wavefarm/Internet-Radio-Toolkit/Arduino/InternetRadioSketch/src/ToolkitFiles/ToolkitFiles.cpp

//
// ToolkitFiles.cpp

#include <FS.h>

//#include <LittleFS.h>
//#define TOOLFS LittleFS

//#include <LITTLEFS.h>
//#define TOOLFS LITTLEFS

#include "../ToolkitLittleFS/ToolkitLittleFS.h"
#define TOOLFS ToolkitLittleFS

#include "ToolkitFiles.h"

boolean ToolkitFiles::begin()
{
    if (!TOOLFS.begin(false)) {
        Serial.println("Flash Storage will be reformatted!");
        Serial.println("This may take a while ..");
        if (!TOOLFS.format()) {
            Serial.println("Error formatting Flash Storage!");
            return false;
        } else { // formatted okay
            delay(100);
            return TOOLFS.begin(false);
        }
    }
    return true; // formats the flash if it isn't formatted
} // returns false if the file system doesn't mount

//
// Some DOCS:
//
// size_t actual = file.readBytes(char *buffer, size_t length);
// int avail = file.available(); .. not sure if this is the same as filesize
// void file.close();
// boolean file.isDirectory();
// size_t file.size();
// size_t file.write(char *buffer, size_t length);
//
// boolean FS.exists(const char *path);
// File FS.open(const char *path, int mode=FILE_READ, const bool create=false);
// mode can also be FILE_WRITE or FILE_APPEND
// NOTE: the headers available online differ from the headers used by the IDE
// bool create is not part of the open() prototype!

boolean ToolkitFiles::fileExists(const char *path)
{
    return TOOLFS.exists(path);
}

char* ToolkitFiles::fileReadAll(const char *path, char *buffer,
    size_t size, size_t *actual)
{
    *actual = 0;
    File f = TOOLFS.open(path);
    if(!f || f.isDirectory()){
        return NULL;
    }
    size_t length = f.size();
    if (length > (size-1)) {
        Serial.print("Filesize is too big .. ");
        Serial.println(path);
        f.close();
        return NULL;
    }

    char *p = buffer;
    size_t remaining = length;
    size_t a;
    while (remaining) {
        a = f.readBytes(p, remaining);
        p = p + a;
        remaining = remaining - a;
    }
    f.close();
    buffer[length] = 0;
    *actual = length;
    return buffer;
}

void ToolkitFiles::fileReadToSerial(const char *path)
{
    Serial.printf("Reading file: %s\r\n", path);

    File f = TOOLFS.open(path);
    if(!f || f.isDirectory()){
        Serial.println("− failed to open file for reading");
        return;
    }

    Serial.println("− read from file:");
    while(f.available()){
        Serial.write(f.read());
    }
}

boolean ToolkitFiles::fileWrite(const char *path, const char *buffer,
    size_t size, boolean append)
{
    File f;
    if (append) {
        f = TOOLFS.open(path, FILE_APPEND);
    } else {
        f = TOOLFS.open(path, FILE_WRITE);
    }
    if (!f) {
        return false;
    }
    const char *p = buffer;
    size_t remaining = size;
    size_t actual;
    while (remaining) {
        actual = f.write((uint8_t *) p, remaining);
        p = p + actual;
        remaining = remaining - actual;
    }
    f.close();
    return true;
}

File ToolkitFiles::fileOpen(const char *path, const char *mode)
{
    return TOOLFS.open(path, mode);
}

//
// Settings
const char *SETTINGS_PATHNAME = "/settings.txt";
static char settings_buffer[ToolkitFiles::MAX_SETTINGS_SIZE];

boolean ToolkitFiles::loadSettings()
{
    size_t length;
    char *buffer = fileReadAll(SETTINGS_PATHNAME, settings_buffer, MAX_SETTINGS_SIZE, &length);
    if (buffer && length) {
        SettingItem::loadSettingsFromBuffer(buffer, length);
        return true;
    }
    return false;
}

void ToolkitFiles::saveSettings()
{
    size_t actual = SettingItem::saveAll(settings_buffer, MAX_SETTINGS_SIZE);
    if (actual) {
        fileWrite(SETTINGS_PATHNAME, settings_buffer, actual);
    }
}

/*
    REFERENCE CODE
*/

/*
//  listDir(SPIFFS, "/", 0);
//  readFile(SPIFFS, "/test.txt");

//--------------
void listDir(fs::FS &fs, const char * dirname, uint8_t levels){
   Serial.printf("Listing directory: %s\r\n", dirname);

   File root = fs.open(dirname);
   if(!root){
      Serial.println("− failed to open directory");
      return;
   }
   if(!root.isDirectory()){
      Serial.println(" − not a directory");
      return;
   }

   File file = root.openNextFile();
   while(file){
      if(file.isDirectory()){
         Serial.print("  DIR : ");
         Serial.println(file.name());
         if(levels){
            listDir(fs, file.name(), levels -1);
         }
      } else {
         Serial.print("  FILE: ");
         Serial.print(file.name());
         Serial.print("\tSIZE: ");
         Serial.println(file.size());
      }
      file = root.openNextFile();
   }
}

void readFile(fs::FS &fs, const char * path){
   Serial.printf("Reading file: %s\r\n", path);

   File file = fs.open(path);
   if(!file || file.isDirectory()){
       Serial.println("− failed to open file for reading");
       return;
   }

   Serial.println("− read from file:");
   while(file.available()){
      Serial.write(file.read());
   }
}
*/
//-----------

//
// END OF ToolkitFiles.cpp
