wavefarm/Internet-Radio-Toolkit/Arduino/InternetRadioSketch/src/ToolkitVLSI/VS1063a_encpatches.h

#ifndef VS1063A_PLUGIN_H
#define VS1063A_PLUGIN_H

#define PLUGIN_SIZE 2276

const uint16_t vs1063a_plugin[] = { /* Compressed plugin */
	0x0007,0x0001, /*copy 1*/
	0x8050,
	0x0006,0x08dc, /*copy 2268*/
	0x0000,0x0000,0x0006,0x8155,0x3d00,0x0024,0x0000,0x8795,
	0xf400,0x5540,0x0000,0x08d5,0xf400,0x5740,0x0006,0x2016,
	0x000f,0xd9cf,0x0000,0x170e,0x280f,0xd1c0,0x0000,0x004d,
	0x0006,0xc797,0x0001,0xf400,0x3009,0x3c00,0x0030,0x0157,
	0x3f00,0x0024,0x280f,0xdb45,0x0000,0x0dc0,0x0007,0x8b97,
	0x0008,0x0000,0x3f00,0x0024,0x0006,0xa717,0x0fff,0xff00,
	0x3009,0x3c80,0x0fff,0xfe00,0x3009,0x3c00,0x0030,0x02d5,
	0x3500,0x0024,0x4080,0x0024,0x0031,0x6b0f,0x2800,0x1c95,
	0x0000,0x4040,0x3d00,0x0024,0x0000,0x1d8e,0x0000,0x004d,
	0x2908,0x73c0,0x0030,0x0480,0x0000,0x0141,0x6012,0x0024,
	0x0000,0x0024,0x2800,0x1f04,0x0000,0x0201,0x6010,0x0024,
	0x0031,0xb4cf,0x0000,0x200e,0x2831,0x6b40,0x0000,0x004d,
	0x3463,0x0024,0x2900,0xd480,0x34a0,0x8024,0x0031,0xbd0f,
	0x0000,0x21ce,0x2831,0xb500,0x0000,0x004d,0x0006,0x9a17,
	0x3701,0x0024,0x0008,0x7a17,0x449a,0x1fc4,0x0000,0x0024,
	0x2800,0x2555,0x448a,0x1cc4,0x3463,0x0024,0x2800,0x2544,
	0x34a1,0x4024,0x0000,0x0400,0x3f00,0x0024,0x2908,0xf780,
	0x3613,0x0024,0x3100,0x0024,0xf200,0x0024,0xf200,0x0024,
	0xf200,0x0024,0xf200,0x0024,0x0031,0xc08f,0x0000,0x278e,
	0x2831,0xbd40,0x0000,0x190d,0x0031,0xc98f,0x2831,0xc2c5,
	0x0000,0x2b0e,0x0000,0x0141,0x6012,0x0ccc,0x0008,0x0001,
	0x2831,0xc285,0x0000,0x0024,0x0031,0x27cf,0x0000,0x2a8e,
	0x2831,0xd5c0,0x0000,0x190d,0x2800,0xf800,0x0000,0x190d,
	0x2935,0x74c0,0x0000,0x0024,0x0000,0x2c95,0x0008,0xdfd7,
	0x2831,0xccc0,0x3f05,0x4024,0x0006,0x0017,0x3f12,0x184c,
	0x3f13,0x7800,0x0000,0x0740,0x2911,0xa7c0,0x3f13,0x8024,
	0x4080,0x3c0f,0x0000,0x0024,0x2800,0x39d5,0x3009,0x1bc0,
	0x0000,0x39c8,0x0000,0x004d,0x0035,0xe5cf,0x2835,0xb7c0,
	0x0000,0x304e,0x0000,0x008d,0x0035,0xc6cf,0x0000,0x34ce,
	0x2835,0xc241,0x0000,0x0041,0x4190,0x110c,0xb886,0xb300,
	0x0000,0x04cd,0x0035,0xee0f,0x2835,0xe780,0x0000,0x330e,
	0x0000,0x0485,0x635a,0x0024,0x0000,0x304e,0x2800,0x3255,
	0x0035,0xe5cf,0x0000,0x0805,0x2a35,0xee40,0x0000,0x008d,
	0x0000,0x304e,0x0035,0xe5cf,0x2835,0xc988,0x0000,0x0024,
	0x0000,0x03d5,0x3483,0x184c,0x003f,0xfc55,0xb888,0x4511,
	0x0000,0x3b8e,0x0039,0xaf0f,0x0000,0x058d,0x2939,0x87c0,
	0x3483,0x0024,0x2900,0x3dc0,0x3613,0x0024,0x0000,0x008d,
	0x0000,0x304e,0x0035,0xe5cf,0x2a35,0xc980,0x0006,0x0017,
	0x3712,0x0024,0x3713,0x4024,0x3713,0x8024,0x3703,0xc024,
	0x2000,0x0000,0x0000,0x0024,0x000d,0x91d7,0x3700,0x4024,
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
	0x000a,0x0001, /*copy 1*/
	0x0050
};

#endif

// END OF VS1063a_encpatches.h
