wavefarm/Internet-Radio-Toolkit/Arduino/InternetRadioSketch/src/ToolkitVLSI/VS1063a_patches.h

#ifndef VS1063A_PLUGIN_H
#define VS1063A_PLUGIN_H

#define PLUGIN_SIZE 7384

const uint16_t vs1063a_plugin[] = { /* Compressed plugin */
	0x0007,0x0001, /*copy 1*/
	0x8050,
	0x0006,0x19be, /*copy 6590*/
	0x0000,0x0000,0x0006,0x8155,0x3d00,0x0024,0x0001,0x3695,
	0xf400,0x5540,0x0000,0x0015,0xf400,0x5740,0x0001,0x36d5,
	0xf400,0x5540,0x0000,0x08d5,0xf400,0x5740,0x0000,0xded7,
	0x2800,0x1b80,0x0000,0x0855,0x0000,0x0000,0x0000,0x0000,
	0x3613,0x0024,0x3e00,0x8024,0x0000,0x02c2,0x6124,0x0024,
	0x0000,0x0024,0x2800,0x1b05,0x4192,0x1bc2,0x0000,0x0041,
	0x2000,0x0015,0x0030,0x0317,0x2000,0x0000,0x3f00,0x4024,
	0x2000,0x0000,0x0000,0x0000,0xf400,0x55c0,0xf400,0x5740,
	0x0006,0x2016,0x000f,0xd9cf,0x0000,0x1d4e,0x280f,0xd1c0,
	0x0000,0x004d,0x0006,0xc797,0x0001,0xf400,0x3009,0x3c00,
	0x0030,0x0157,0x3f00,0x0024,0x280f,0xdb45,0x0000,0x0dc0,
	0x0007,0x8b97,0x0008,0x0000,0x3f00,0x0024,0x0006,0xa717,
	0x0fff,0xff00,0x3009,0x3c80,0x0fff,0xfe00,0x3009,0x3c00,
	0x0030,0x02d5,0x3500,0x0024,0x4080,0x0024,0x0031,0x6b0f,
	0x2800,0x22d5,0x0000,0x4040,0x3d00,0x0024,0x0000,0x23ce,
	0x0000,0x004d,0x2908,0x73c0,0x0030,0x0480,0x0000,0x0141,
	0x6012,0x0024,0x0000,0x0024,0x2800,0x2544,0x0000,0x0201,
	0x6010,0x0024,0x0031,0xb4cf,0x0000,0x264e,0x2831,0x6b40,
	0x0000,0x004d,0x3463,0x0024,0x2902,0x7900,0x34a0,0x8024,
	0x0031,0xbd0f,0x0000,0x280e,0x2831,0xb500,0x0000,0x004d,
	0x0006,0x9a17,0x3701,0x0024,0x0008,0x7a17,0x449a,0x1fc4,
	0x0000,0x0024,0x2800,0x2b95,0x448a,0x1cc4,0x3463,0x0024,
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
	0x0010,0xfffd,0x1a72,0x1a70,
	0x0007,0x0001, /*copy 1*/
	0x5800,
	0x0006, 0x8008, 0x0000, /*Rle(8)*/
	0x0006,0x0009, /*copy 9*/
	0x4e13,0x1d39,0x7fff,0x0001,0xc01c,0x0002,0x0002,0x0000,
	0xc01b,
	0x000a,0x0001, /*copy 1*/
	0x0050
};

#endif

// END OF VS1063a_patches.h
