wavefarm/Internet-Radio-Toolkit/Arduino/InternetRadioSketch/src/ToolkitWiFi/icy_stream.h

//----------------------------------------------------------------------------------------------
//
//	icy.h
//
//	February 2019
//
//----------------------------------------------------------------------------------------------

#ifndef _ICY_H_
#define _ICY_H_

// Create a request header from setting, open connection, etc.
boolean icy_start_stream(WiFiClient *client);

#endif

//----------------------------------------------------------------------------------------------
// END OF icy.h
//----------------------------------------------------------------------------------------------
