wavefarm/Internet-Radio-Toolkit/Arduino/InternetRadioSketch/src/parsingTools.h

//
// parsingTools.h

//
// Some simple inline utils .. cause it's faster than using Arduino Strings

inline boolean isDigit(const char c, int *dots)
{
    if ('.'==c) { (*dots)++; return true; }
    return ((c>='0') && (c<='9'));
}

inline int isNumeric(const char *s)
{
    int dots = 0;
    while (*s) {
        if (!isDigit(*s, &dots)) {
            return 0;
        }
        s++;
    }
    return 1+dots;
}

inline const char *checkForEnd(const char *text, const char *end)
{
    if (text>=end) { return NULL; }
    return text;
}

inline const char *clearNewlines(const char *text)
{
    while (true) {
        switch (*text) {
            case '\n' :
            case '\r' :
                text++;
                break;
            default :
                return text;
                break;
        }
    }
}

inline const char *clearWhitespace(const char *text)
{
    while(true) {
        switch (*text) {
            case '\t' :
            case ' ' :
            case '=' :
                text++;
                break;
            default :
                return text;
                break;
        }
    }
}

// returns pointer to 1 character after the string
inline const char *findEndOfString(const char *text)
{
    while (true) {
        switch (*text) {
            case '\0' :
            case '\t' :
            case '\n' :
            case ' ' :
            case '=' :
                return text;
                break;
            default :
                text++;
                break;
        }
    }
}

inline const char *findEndOfValue(const char *text)
{
    const char *space = 0; // position of a terminating space, 0 for none
    while (true) {
        switch (*text) {
            case '\0' :             // terminator characters
            case '\t' :
            case '\n' :
                if (0 != space) {
                    return space;
                }
                return text;
                break;
            case ' ' :              // space is internal or tail (trimmed)
                if (0 == space) {
                    space = text;
                }
                text++;
                break;
            default :               // characters to include in the value
                space = 0;
                text++;
                break;
        }
    }
}

inline boolean isTerminator(const char *text)
{
    switch (*text) {
        case '\0' :
        case '\n' :
        case '\r' : // maybe someone uses and old text editor
            return true;
            break;
    }
    return false;
}

inline const char *skipToTerminatar(const char *text)
{
    while (!isTerminator(text)) { text++; }
    return text;
}

inline const char *findTwoEndlines(const char *buffer)
{
    uint32_t n = 0;
    while (*buffer) {
        switch (*buffer) {
            case '\n' :
                n++;
            case '\r' :
                break;
            default :
                n = 0;
                break;
        }
        buffer++;
        if (2==n) {
            return buffer;
        }
    }
    return NULL;
}

//
// END OF parsingTools.h
